breilly1296/Super-8-Camera/transport_18fps_preview.png

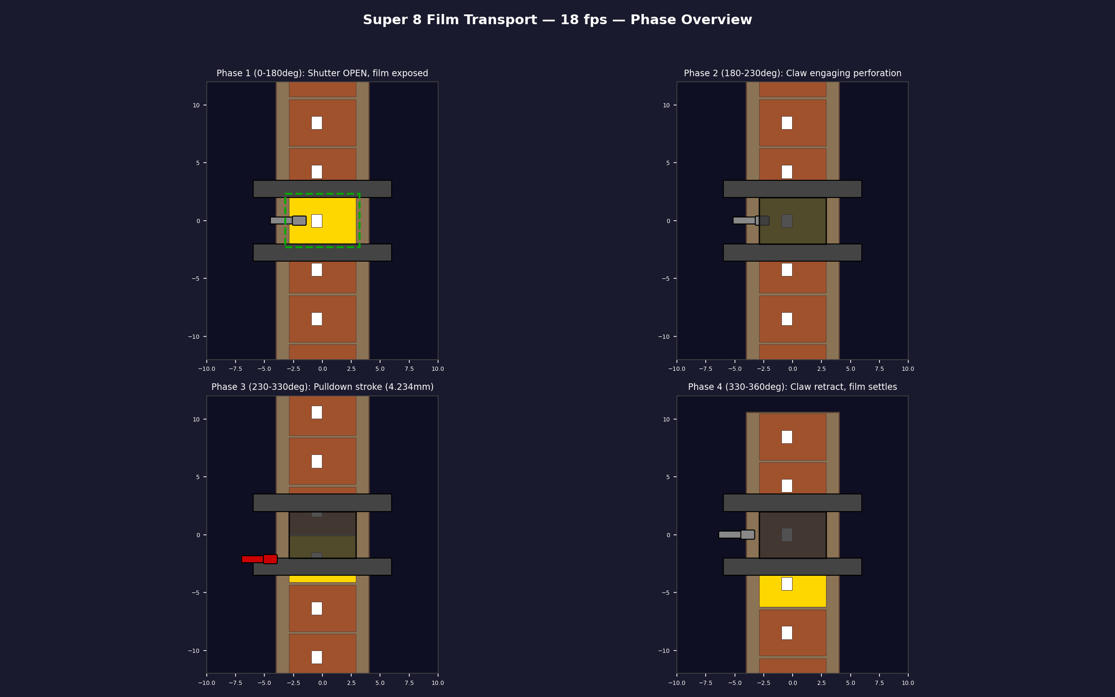
transport_18fps_preview.png
