breilly1296/Super-8-Camera/pid_test_18fps.png

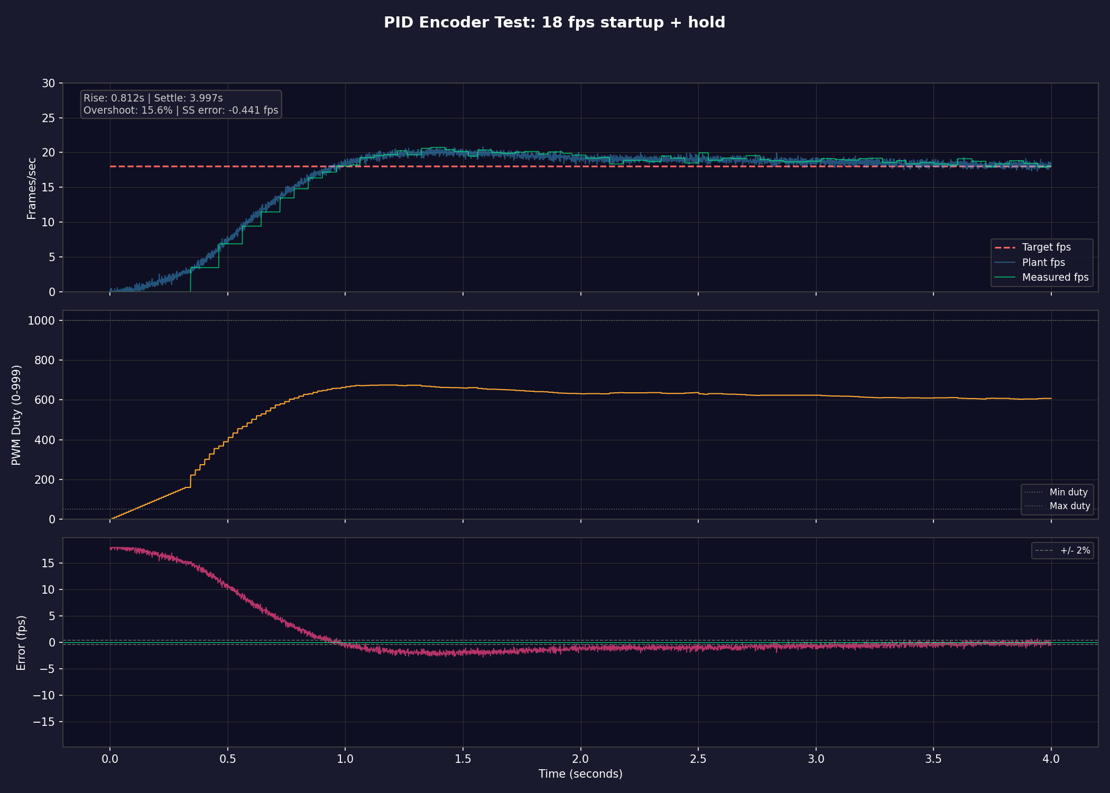
pid_test_18fps.png
