breilly1296/Super-8-Camera/pid_test_switch.png

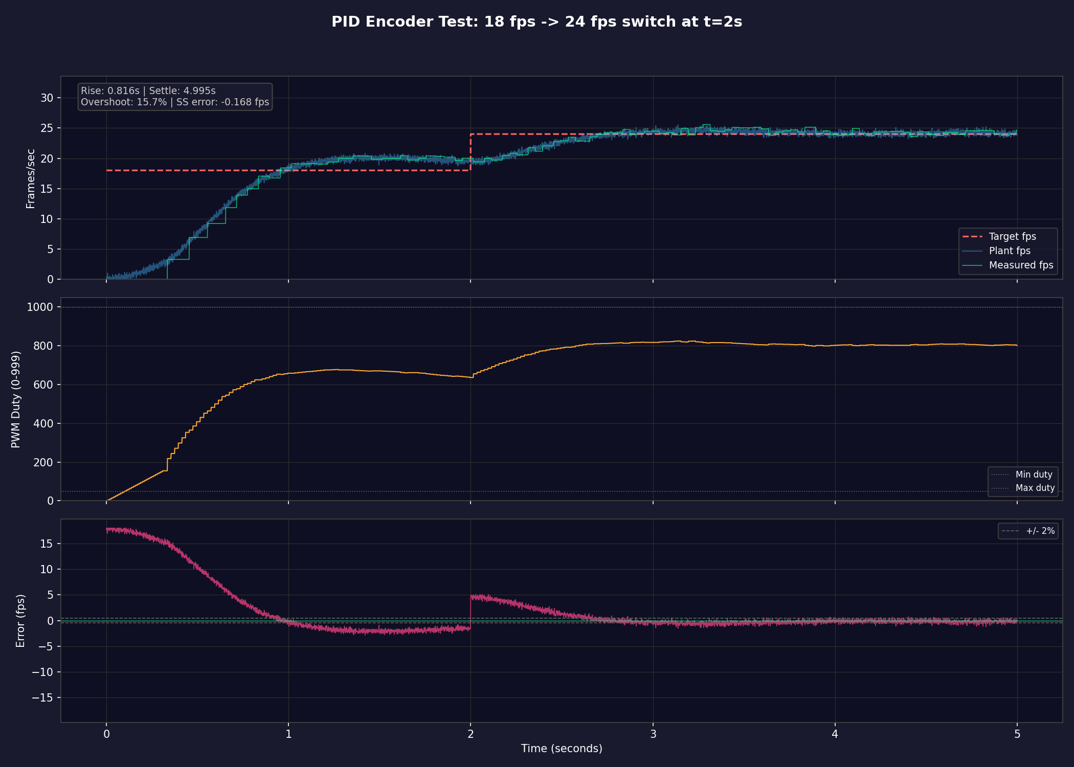
pid_test_switch.png
