breilly1296/Super-8-Camera/super8_camera.kicad_sch

## KiCad design super8_camera.kicad_sch (2026-03-06)

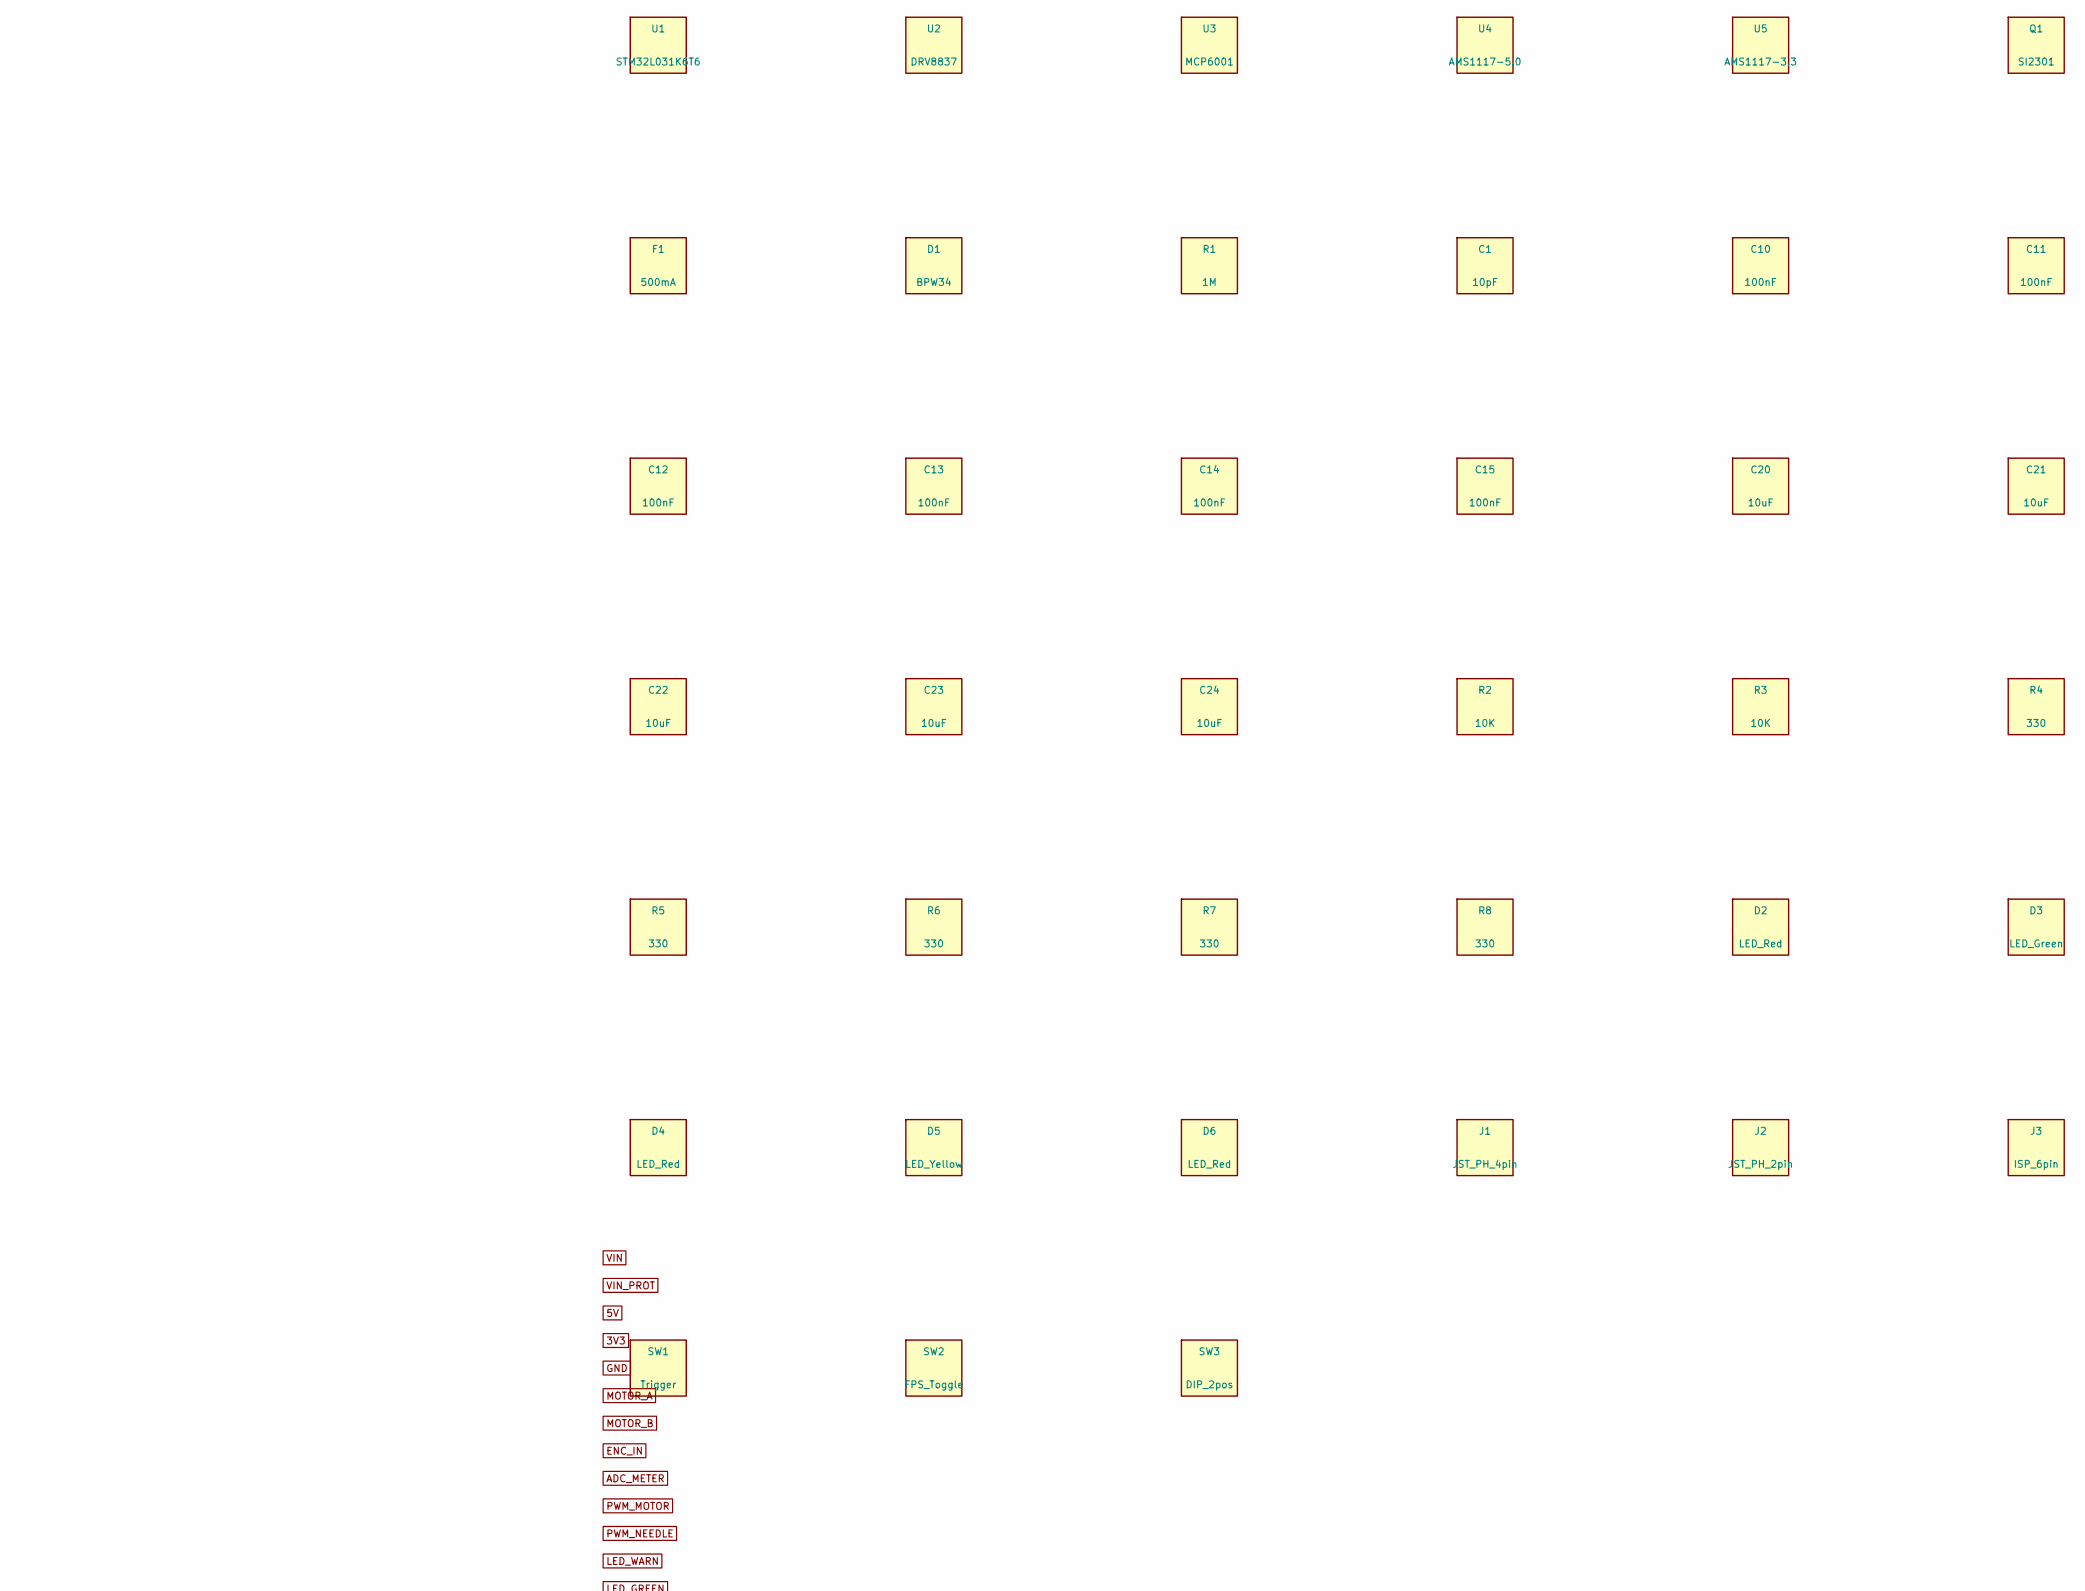
[picture p12: schematic super8_camera.kicad_sch, part in row 1, column 1]

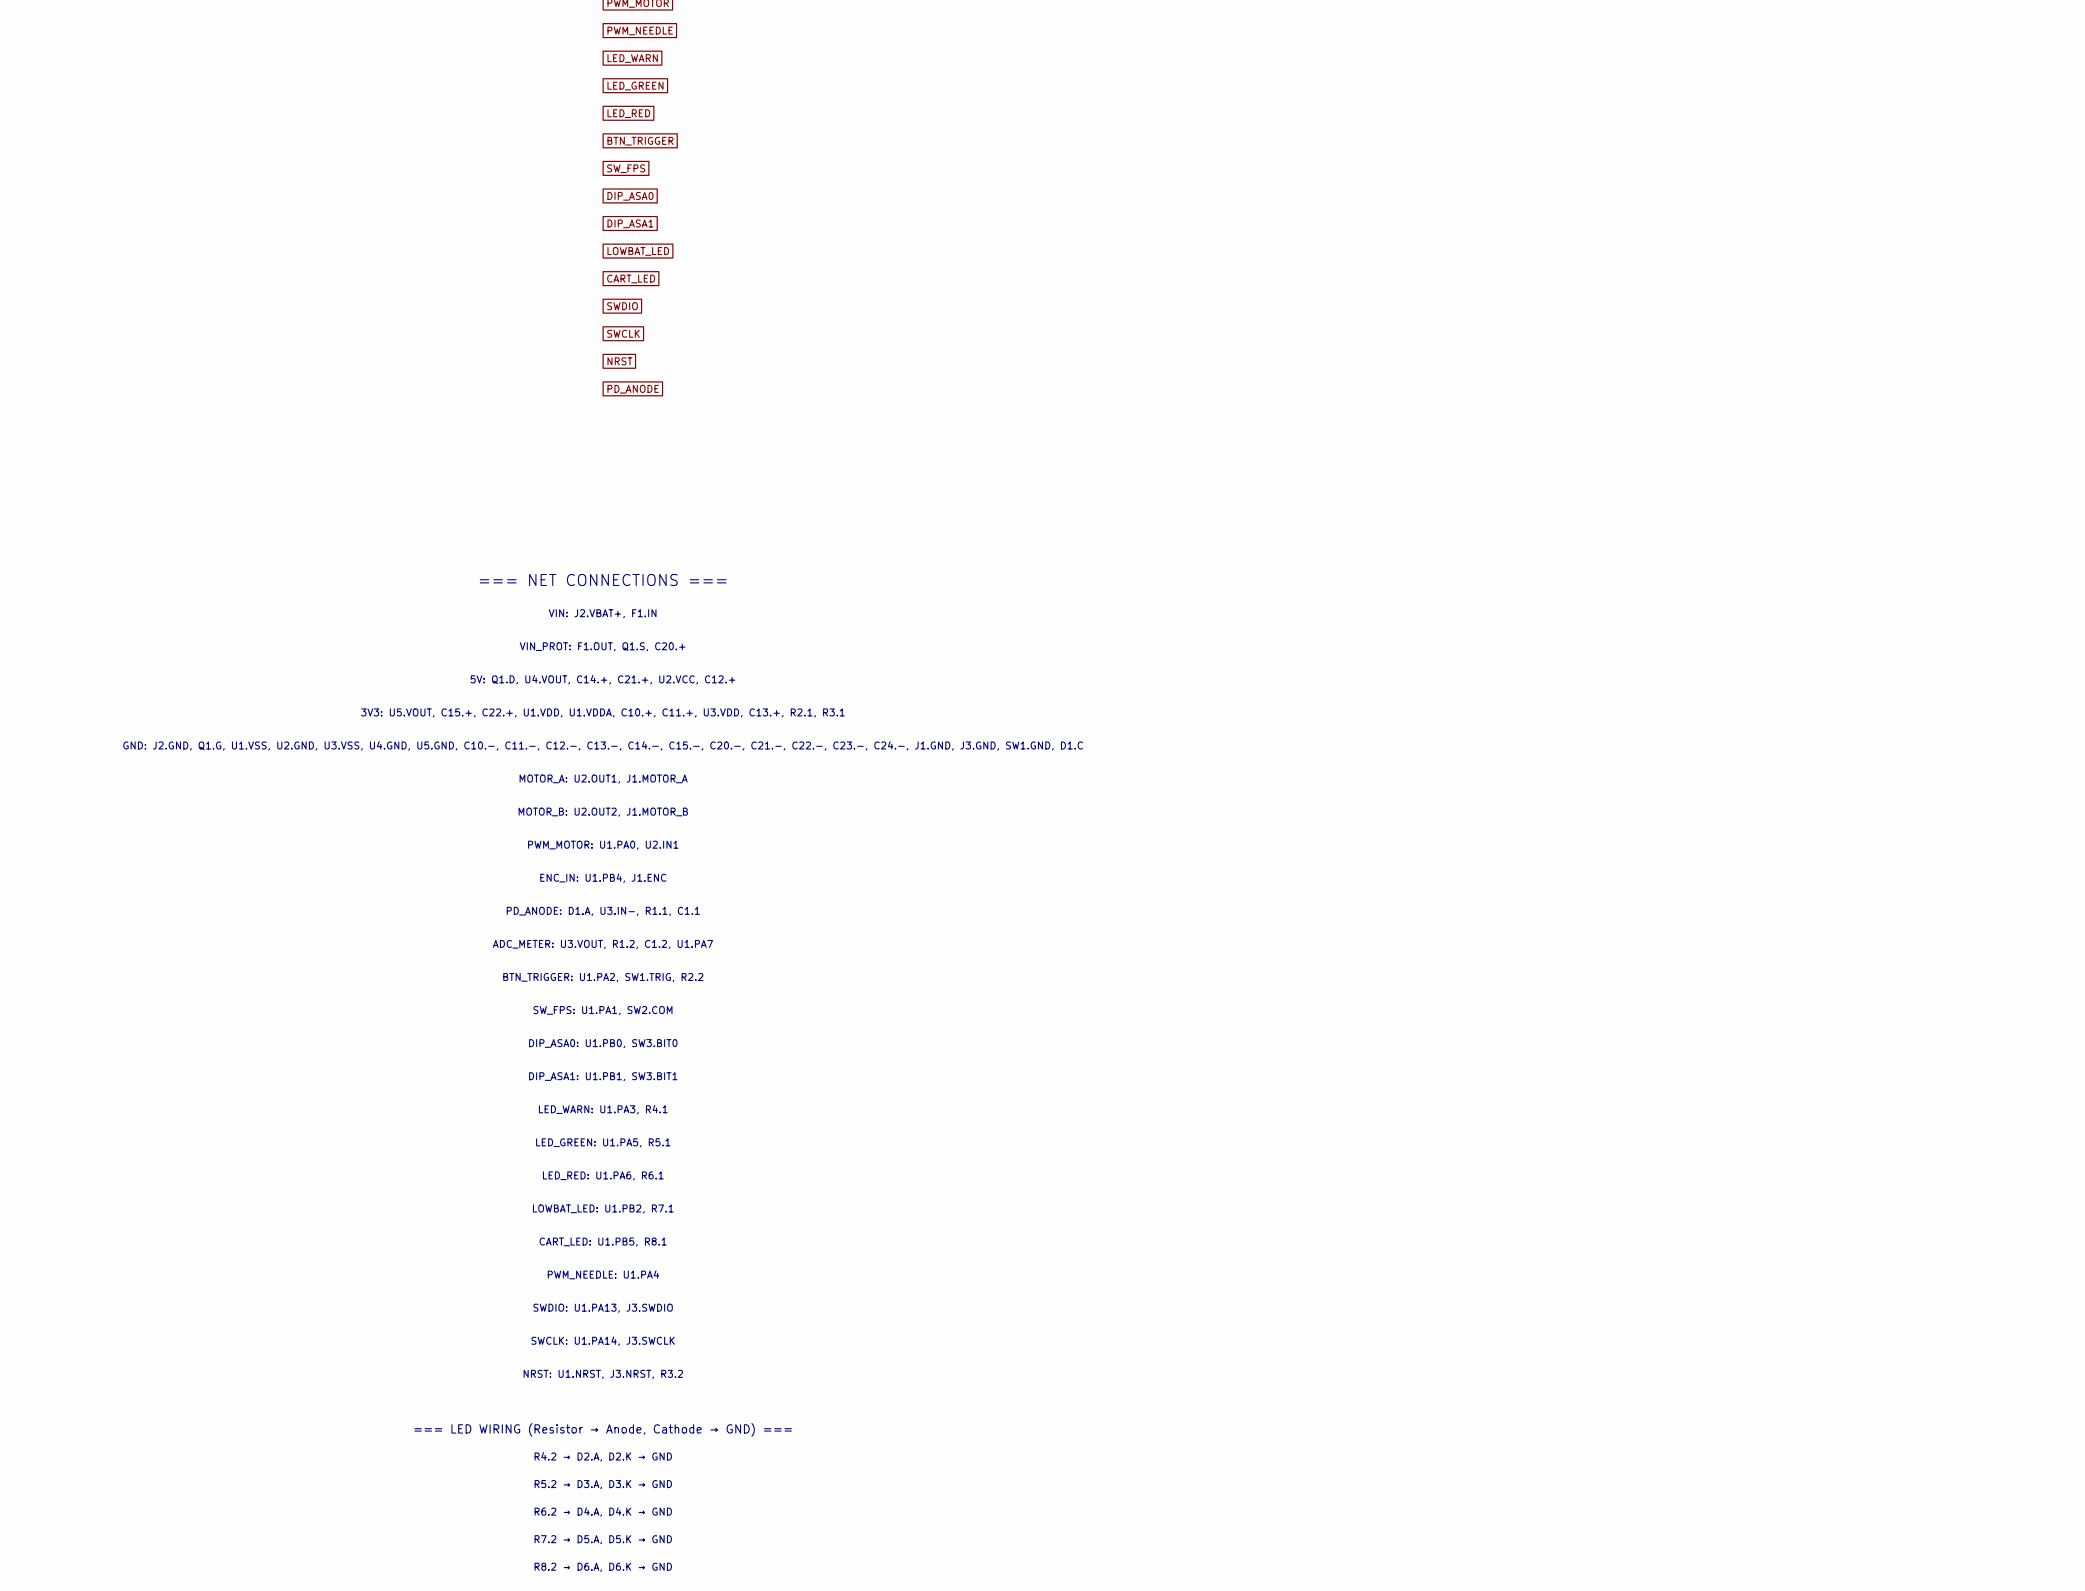
[picture p13: schematic super8_camera.kicad_sch, part in row 2, column 1]

Parts:
C1: 10pF; C_0603
C10, C11, C12, C13, C14, C15: 100nF; C_0603
C20, C21, C22, C23, C24: 10uF; C_0805
D1: BPW34; BPW34_DIL; MPN BPW34
D2, D4, D6: LED_Red; LED_0603
D3: LED_Green; LED_0603
D5: LED_Yellow; LED_0603
F1: 500mA; Fuse_1206; MPN MF-MSMF050-2
J1: JST_PH_4pin; JST_PH_B4B-PH-K_1x04_P2.00mm_Vertical; MPN B4B-PH-K-S
J2: JST_PH_2pin; JST_PH_B2B-PH-K_1x02_P2.00mm_Vertical; MPN B2B-PH-K-S
J3: ISP_6pin; PinHeader_2x03_P2.54mm_Vertical
Q1: SI2301; SOT-23; MPN SI2301CDS-T1-GE3
R1: 1M; R_0603
R2, R3: 10K; R_0603
R4, R5, R6, R7, R8: 330; R_0603
SW1: Trigger; SW_Push_SPST
SW2: FPS_Toggle; SW_Toggle_SPDT
SW3: DIP_2pos; DIP-02_SMD
U1: STM32L031K6T6; LQFP-32_7x7mm_P0.8mm; MPN STM32L031K6T6
U2: DRV8837; WSON-8_2x2mm_P0.5mm; MPN DRV8837DSGR
U3: MCP6001; SOT-23-5; MPN MCP6001T-I/OT
U4: AMS1117-5.0; SOT-223-3; MPN AMS1117-5.0
U5: AMS1117-3.3; SOT-223-3; MPN AMS1117-3.3

Notes on the sheet:
=== NET CONNECTIONS ===
VIN: J2.VBAT+, F1.IN
VIN_PROT: F1.OUT, Q1.S, C20.+
5V: Q1.D, U4.VOUT, C14.+, C21.+, U2.VCC, C12.+
3V3: U5.VOUT, C15.+, C22.+, U1.VDD, U1.VDDA, C10.+, C11.+, U3.VDD, C13.+, R2.1, R3.1
GND: J2.GND, Q1.G, U1.VSS, U2.GND, U3.VSS, U4.GND, U5.GND, C10.-, C11.-, C12.-, C13.-, C14.-, C15.-, C20.-, C21.-, C22.-, C23.-, C24.-, J1.GND, J3.GND, SW1.GND, D1.C
MOTOR_A: U2.OUT1, J1.MOTOR_A
MOTOR_B: U2.OUT2, J1.MOTOR_B
PWM_MOTOR: U1.PA0, U2.IN1
ENC_IN: U1.PB4, J1.ENC
PD_ANODE: D1.A, U3.IN-, R1.1, C1.1
ADC_METER: U3.VOUT, R1.2, C1.2, U1.PA7
BTN_TRIGGER: U1.PA2, SW1.TRIG, R2.2
SW_FPS: U1.PA1, SW2.COM
DIP_ASA0: U1.PB0, SW3.BIT0
DIP_ASA1: U1.PB1, SW3.BIT1
LED_WARN: U1.PA3, R4.1
LED_GREEN: U1.PA5, R5.1
LED_RED: U1.PA6, R6.1
LOWBAT_LED: U1.PB2, R7.1
CART_LED: U1.PB5, R8.1
PWM_NEEDLE: U1.PA4
SWDIO: U1.PA13, J3.SWDIO
SWCLK: U1.PA14, J3.SWCLK
NRST: U1.NRST, J3.NRST, R3.2
=== LED WIRING (Resistor → Anode, Cathode → GND) ===
R4.2 → D2.A, D2.K → GND
R5.2 → D3.A, D3.K → GND
R6.2 → D4.A, D4.K → GND
R7.2 → D5.A, D5.K → GND
R8.2 → D6.A, D6.K → GND
