breilly1296/Super-8-Camera/super8cam/parts/main_shaft.py

"""Main shaft — stepped hardened steel shaft carrying shutter, cam, and gear.

The main shaft is the mechanical backbone of the camera.  It receives power
from the gearbox at one end, carries the pulldown cam and secondary eccentric
in the middle, and drives the shutter disc near the front.  An encoder disc
at the far end provides position feedback.

Material: AISI 4140 chrome-moly steel, through-hardened HRC 28-32.
Bearing seats ground to h6 tolerance.

All dimensions from master_specs.

Shaft layout (Z axis, rear=−Z to front=+Z):
  Section 1:  Gear end       3mm dia × 8mm   (keyway for driven gear)
  Shoulder:   3mm → 4mm      0.3mm × 45° chamfer
  Section 2:  Bearing seat 1 4mm dia × 4mm   (694ZZ press-fit, h6)
  Section 3:  Cam section    4mm dia × 6mm   (pulldown cam + eccentric, keyed)
  Section 4:  Bearing seat 2 4mm dia × 4mm   (694ZZ press-fit, h6)
  Section 5:  Shutter seat   4mm dia × 3mm   (shutter disc, keyed)
  Shoulder:   4mm → 3mm      0.3mm × 45° chamfer
  Section 6:  Encoder end    3mm dia × 4mm   (encoder disc, M3 thread at tip)
  Total:      8+4+6+4+3+4 = 29mm usable + shoulders ≈ 30mm
"""

import math
import cadquery as cq
from super8cam.specs.master_specs import (
    CAMERA, MATERIALS, MATERIAL_USAGE, BEARINGS, SHAFT_DIMS,
)

MATERIAL = MATERIALS[MATERIAL_USAGE["main_shaft"]]

# =========================================================================
# SHAFT SECTION DIMENSIONS
# =========================================================================

# Section 1: Gear end (rear)
SEC1_DIA = SHAFT_DIMS.sec1_dia          # 3.0 mm
SEC1_LEN = SHAFT_DIMS.sec1_len          # 8.0 mm
SEC1_KEYWAY_W = SHAFT_DIMS.sec1_keyway_w     # 0.6 mm
SEC1_KEYWAY_DEPTH = SHAFT_DIMS.sec1_keyway_depth  # 0.3 mm

# Section 2: Bearing seat 1
SEC2_DIA = CAMERA.shaft_dia             # 4.0 mm (already uses CAMERA)
SEC2_LEN = BEARINGS["main_shaft"].width  # 4.0 mm (already uses BEARINGS)

# Section 3: Cam section
SEC3_DIA = CAMERA.shaft_dia
SEC3_LEN = SHAFT_DIMS.sec3_len          # 6.0 mm
SEC3_KEYWAY_W = SHAFT_DIMS.sec3_keyway_w     # 1.0 mm
SEC3_KEYWAY_DEPTH = SHAFT_DIMS.sec3_keyway_depth  # 0.5 mm

# Section 4: Bearing seat 2
SEC4_DIA = CAMERA.shaft_dia
SEC4_LEN = BEARINGS["main_shaft"].width
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
